UnexpectedMaker/ReflowMaster/Code/Reflow_Master_v2/FlashStorage.cpp

/*
  Copyright (c) 2015 Arduino LLC.  All right reserved.
  Written by Cristian Maglie

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
  You should have received a copy of the GNU Lesser General Public
  License along with this library; if not, write to the Free Software
  Foundation, Inc., 51 Franklin St, Fifth Floor, Boston, MA  02110-1301  USA
*/

#include "FlashStorage.h"

static const uint32_t pageSizes[] = { 8, 16, 32, 64, 128, 256, 512, 1024 };

FlashClass::FlashClass(const void *flash_addr, uint32_t size) :
  PAGE_SIZE(pageSizes[NVMCTRL->PARAM.bit.PSZ]),
  PAGES(NVMCTRL->PARAM.bit.NVMP),
  MAX_FLASH(PAGE_SIZE * PAGES),
  ROW_SIZE(PAGE_SIZE * 4),
  flash_address((volatile void *)flash_addr),
  flash_size(size)
{
}

static inline uint32_t read_unaligned_uint32(const void *data)
{
  union {
    uint32_t u32;
    uint8_t u8[4];
  } res;
  const uint8_t *d = (const uint8_t *)data;
  res.u8[0] = d[0];
  res.u8[1] = d[1];
  res.u8[2] = d[2];
  res.u8[3] = d[3];
  return res.u32;
}

void FlashClass::write(const volatile void *flash_ptr, const void *data, uint32_t size)
{
  // Calculate data boundaries
  size = (size + 3) / 4;
  volatile uint32_t *dst_addr = (volatile uint32_t *)flash_ptr;
  const uint8_t *src_addr = (uint8_t *)data;

  // Disable automatic page write
  NVMCTRL->CTRLB.bit.MANW = 1;

  // Do writes in pages
  while (size) {
    // Execute "PBC" Page Buffer Clear
    NVMCTRL->CTRLA.reg = NVMCTRL_CTRLA_CMDEX_KEY | NVMCTRL_CTRLA_CMD_PBC;
    while (NVMCTRL->INTFLAG.bit.READY == 0) { }

    // Fill page buffer
    uint32_t i;
    for (i=0; i<(PAGE_SIZE/4) && size; i++) {
      *dst_addr = read_unaligned_uint32(src_addr);
      src_addr += 4;
      dst_addr++;
      size--;
    }

    // Execute "WP" Write Page
    NVMCTRL->CTRLA.reg = NVMCTRL_CTRLA_CMDEX_KEY | NVMCTRL_CTRLA_CMD_WP;
    while (NVMCTRL->INTFLAG.bit.READY == 0) { }
  }
}

void FlashClass::erase(const volatile void *flash_ptr, uint32_t size)
{
  const uint8_t *ptr = (const uint8_t *)flash_ptr;
  while (size > ROW_SIZE) {
    erase(ptr);
    ptr += ROW_SIZE;
    size -= ROW_SIZE;
  }
  erase(ptr);
}

void FlashClass::erase(const volatile void *flash_ptr)
{
  NVMCTRL->ADDR.reg = ((uint32_t)flash_ptr) / 2;
  NVMCTRL->CTRLA.reg = NVMCTRL_CTRLA_CMDEX_KEY | NVMCTRL_CTRLA_CMD_ER;
  while (!NVMCTRL->INTFLAG.bit.READY) { }
}

void FlashClass::read(const volatile void *flash_ptr, void *data, uint32_t size)
{
  memcpy(data, (const void *)flash_ptr, size);
}
